jes5199/poison-oak-tokens/20mm/heightmap_20mm_bead_L3b_deep.png

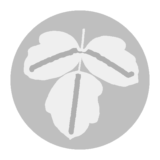
20mm/heightmap_20mm_bead_L3b_deep.png
