jes5199/poison-oak-tokens/40mm/heightmap_40mm_stemin_thick.png

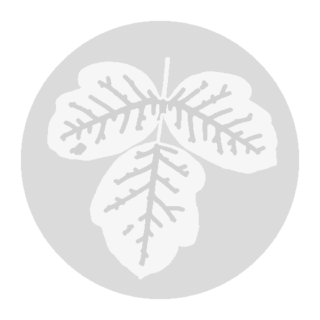
40mm/heightmap_40mm_stemin_thick.png
